m9h/freeeeg128/paper/paper.pdf

## FreeEEG128: Design and Roadmap for an Open-Hardware 128-Channel EEG Acquisition System

Historical lineage, current-state audit, and alpha/beta plan

Morgan Hough¹

1NeuroTechX., morgan.hough@gmail.com

April 2026

Abstract

We present the design state, hardware audit, and alpha-to-beta development roadmap of FreeEEG128, an open-hardware 128-channel scalp electroencephalography acquisition system evolving the NeuroIDSS FreeEEG128-alpha platform. The alpha board pairs an STMicroelectronics STM32H743ZI Cortex-M7 microcontroller with sixteen Texas Instruments ADS131M08 24-bit delta-sigma ADCs distributed across six SPI buses, a timer/DMA cascade providing sample-synchronous chip-select pulses, and a medical-grade digital- and power-isolation barrier between subject and host. The accompanying cap carries 130 dry Ag/AgCl passive electrodes on a 10/5 textile scaffold. We situate the design in the lineage running from Nunez’s biophysical framework through Gevins’ real-time cognitive-state engineering, Tucker’s Geodesic Sensor Net at Electrical Geodesics, Inc., and the active-electrode breakthrough at BioSemi; and we identify Black et al. 2017 (Open Ephys + EEG) as the primary feature-for-feature comparison benchmark. We audit the alpha board’s peripheral inventory, flag the shortcomings of the stock firmware, and present a phased firmware rewrite (packet-format freeze, modular driver layer, first-class impedance mode, device-side timestamping, watchdog and DFU support). We commit to a belt-pack wearable form factor with a cap-mounted passive brain-box; reject the STM32MP2 upgrade path due to battery-weight and EMI regressions; and plan an ESP32-S3 co-processor on a beta revision for CircuitPython-compatible networking, LSL/WebSocket delivery, and an Adafruit-ecosystem surface. Validation against the Black et al. eyes-closed alpha-vs-actiCHamp protocol is proposed as the beta acceptance gate, with integrations targeted for Open Ephys GUI, MNE-CPP, and BrainFlow on day one.

## Contents

1 Introduction | 2
2 Historical lineage | 3

3 Related open-hardware work | 5
4 System architecture | 7
5 Enclosure, form factor, and cabling | 9
6 MCU and companion-processor choice | 9
7 Firmware rewrite | 12
8 Host and application support | 12
9 Validation plan | 14
10 Open questions and next steps | 14
11 Future directions: form-factor variants | 14

## 1 Introduction

High-density electroencephalography was born from three simultaneous mid-1990s breakthroughs: Paul Nunez’s biophysical account of scalp potentials and the corresponding Nyquist-style argument for densely sampling the head [Nunez, 1981, Nunez and Westdorp, 1994]; Alan Gevins’ real-time cognitive-state engineering practice; and the first commercial 256-channel EEG system, built at Neuroscan by Pflieger and Sands [Pflieger and Sands, 1996], followed rapidly by the second 256-channel system at Electrical Geodesics, Inc. (EGI), which commercialized Tucker’s Geodesic Sensor Net [Tucker, 1993]. Three decades later, academic and clinical high-density EEG remains dominated by a handful of closed-ecosystem vendors (BioSemi, Brain Products, ANT Neuro, Compumedics Neuroscan, g.tec, NA300/GTEN, etc.), and the open-hardware movement has only recently approached 100-channel counts.
The open-hardware track itself has matured quickly. OpenBCI (2014) made 8-channel ADS1299 acquisition routinely accessible; Open Ephys (Siegle et al. 2017 [Siegle et al., 2017]) generalized 512-channel multichannel electrophysiology via a plugin GUI; Black et al. 2017 [Black et al., 2017] adapted that platform to 128-channel human EEG and validated it side-by-side against a Brain-Vision actiCHamp clinical amplifier. Cardona-Álvarez et al. 2023 [Cardona-Alvarez et al., 2023] published the most detailed production framework for an open-hardware BCI to date, built on OpenBCI Cyton with a Raspberry Pi acquisition server, distributed Kafka-based message fan-out, and a custom three-layer driver stack; their work documents the OpenBCI Cyton+Daisy 8→16 channel interleaving artifact that FreeEEG128’s synchronized 16×ADS131M08 architecture eliminates. More recent entries — PiEEG, IronBCI, HackEEG, BIOADC, Neurogate OctaFlow — cover an expanding range of channel counts, packaging, and wireless protocols, but none have delivered 128-channel density with full medical-grade isolation, free licensing of both firmware and hardware, and first-class support for the full open real-time stack (Open Ephys GUI + MNE-CPP + BrainFlow + LSL + BIDS-EEG).
FreeEEG128 aims at that gap. The alpha revision (NeuroIDSS, Vivancos 2023 [Vivancos, 2023]) exists as fewer than five physical units worldwide. One is on the author’s bench; the present paper describes the design audit, the firmware-rewrite roadmap, and the planned beta revision.

## 2 Historical lineage

### 2.1 Theoretical foundations — Nunez

Nunez’s book Electric Fields of the Brain [Nunez, 1981] (second edition with Srinivasan [Nunez and Srinivasan, 2006]) remains the canonical biophysical reference. Three arguments continue to shape hardware design: (i) scalp potential is spatially low-pass-filtered relative to cortical sources, with the skull acting as a 2 cm to 3 cm smoothing kernel; (ii) reference electrode choice is not neutral, and software-defined referencing (surface Laplacian, average reference) is required for source-localization work [Nunez and Westdorp, 1994]; and (iii) volume conduction ensures that no scalp sensor sees a single source. Each of these motivates the channel-count race of the 1990s: below roughly 64 electrodes the surface-Laplacian math does not pay off.

### 2.2 Engineering pioneer — Gevins

Alan Gevins founded EEG Systems Laboratory (1980) and SAM Technology (1986), and by the early 1990s had pushed EEG hardware practice toward 64 and 128 channels with sustained real-time cognitive-state analysis. His “deblurring” methods, combining MRI-derived geometry with scalp EEG to estimate cortical-surface potential [Gevins et al., 1997], predate modern source localization and established the protocol templates for sustained-attention and mental-workload studies that the field still uses.

### 2.3 Engineering breakthrough — Tucker and EGI

Don Tucker’s Geodesic Sensor Net [Tucker, 1993], commercialized as Electrical Geodesics, Inc., is the direct ancestor of the FreeEEG128 form factor. The saline-sponge electrode array on a tension-distributed elastic polymer scaffold solved the practical application-workflow problem that had made high-density EEG impractical outside specialist labs: application time dropped from 60+ minutes (paste-based) to approximately five minutes. EGI built the second 256-channel EEG system in the world; the present author served as its first software engineering manager during the mid-1990s. Ramesh Srinivasan, Nunez’s co-author on the second edition of Electric Fields of the Brain [Nunez and Srinivasan, 2006] and now Professor of Cognitive Sciences and Biomedical Engineering at UC Irvine, was an early member of EGI, which is why EGI’s product line shipped with surface-Laplacian and average- reference montaging as first-class software features from the start.

### 2.4 The commercial high-density era

Table 1 summarizes the commercial high-density landscape. Common themes that FreeEEG128 inherits, or explicitly moves past, include a pervasive reliance on proprietary caps, connectors, amps, and software; the emergence of belt-pack amps (ANT, BrainProducts LiveAmp) after a decade of desk-tethered designs; the first high-density active-electrode system at BioSemi in the late 1990s, which remains the standard against which movement-tolerant recording is measured; and the eventual standardization of per-channel impedance-check and reference- flexibility as tablestakes features.

Table 1: Representative commercial high-density EEG vendors. Channel counts are the maxima offered; years are approximate first-introduction.

Vendor | System | Max ch | Era | Notable feature
Neuroscan | SynAmps / Quik-Cap | 256 | early 1990s | First 256-ch system [Pflieger and Sands, 1996]
EGI | Net Amps / Geodesic Sensor Net | 256 | 1992- | Saline-sponge quick-apply cap
BioSemi | ActiveTwo | 256 | late 1990s- | First HD-EEG with active electrodes
BrainProducts | actiCHamp / actiCAP | 256 | 2000s- | BrainVision Recorder ecosystem
ANT Neuro | eego / Waveguard | 256 | 2000s- | Belt-pack amp + dry-alt caps
Compumedics Neuroscan | SynAmps2 / SynAmpsRT | 512 | 2000s- | Clinical mainstay
g.tec | g.USBamp / g.Nautilus | 256 | 2000s- | Modular headbox
g.tec | g.Pangolin / g.HIamp (4×) | 1024 | 2023- | VHD-EEG SOTA flex-PCB active-wet grids; 8.6 mm spacing; 95.2% CS localization vs ECoG [Schreiner et al., 2024]

### 2.5 The very-high-density frontier — g.Pangolin and 1024-channel EEG

A second revolution has been quietly underway since roughly 2020: the move from “HD-EEG” (64–128 channels) to ultra- or very-high- density EEG (VHD-EEG / uHD-EEG, 256–1024+ channels). The theoretical driver is a refinement of Nunez’s spatial-Nyquist argument — Grover and Venkatesh (cited in Schreiner et al. 2024) propose, on information-theoretic grounds, that the scalp’s spatial bandwidth demands not hundreds but thousands of electrode positions to capture all of the information it carries.
The state-of-the-art commercial VHD system is g.tec’s g.Pangolin [Schreiner et al., 2024], a 1024-channel-capable uHD-EEG platform operating at a 256-channel density in the published demonstration. Key specifications:
- Up to 1024 channels via four g.HIamp 256-channel amplifiers.
- Flexible printed-circuit electrode grids of 16 channels each, with gold-plated electrode points arranged at 8.6 mm inter-electrode distance and 5.9 mm electrode diameter.
- An active pre-amplifier per grid (fixed gain 10) before the back-end g.HIamp.
- Wet electrodes with conductive paste (Elefix) under an adhesive layer designed to prevent bridging and crosstalk.
- 24-bit ADC resolution, up to 38.4 kHz sample rate per channel.
- Authors of Schreiner et al. (2024) include Christoph Guger (founder of g.tec) among g.tecaffiliated researchers.

Schreiner et al. use this system at 256-channel density to demonstrate 95.2% classification accuracy of channels as anterior or posterior to the central sulcus via somatosensory-evokedpotential phase-reversal analysis — a level of functional precision previously only achievable with surgically implanted ECoG.
Closely related theoretical and methodological work includes Shirazi, Onton & Makeig (2025) [Shirazi et al., 2025], who simulate scalp EEG from ultra-high-density ECoG to quantify cortex-to-scalp projection patterns; Liu et al. (2018) [Liu et al., 2018], who establish the systematic benefits of density, head modeling, and source localization for reconstructing large-scale brain networks; and Fiedler et al. (2022) [Fiedler et al., 2022], whose 256-channel dry cap covers the dry-electrode side of the VHD spectrum.

Where FreeEEG128 sits in this landscape. We are deliberately not claiming VHD-EEG status. The open-hardware frontier at 256+ channels remains commercial-only as of April 2026. FreeEEG128 occupies the “affordable mid-density open-hardware” niche: higher channel count than OpenBCI (8–16) and Open Ephys + EEG / Black 2017 (64–128), lower than g.Pangolin (1024), at roughly one to two orders of magnitude lower cost than the commercial systems at comparable channel counts. A natural upgrade path (“FreeEEG256”) on the same STM32H743 + ADS131M08 chassis is plausible — thirty-two ADCs across six SPI buses plus a second- stage cable design — and would put open hardware meaningfully closer to the VHD threshold, but that is explicitly not within the present roadmap.

### 2.6 The open-hardware generation

FreeEEG128 sits at the current frontier of open-hardware EEG. Section 3 presents the feature-level comparison in detail.

## 3 Related open-hardware work

Table 2 enumerates the open-hardware EEG projects relevant to FreeEEG128. Two observations matter for design decisions. First, no existing open-hardware project reaches 128 channels without compromising on either licensing (Black et al. 2017 is CC-BY-NC-SA 3.0 IGO, restricting commercial use) or form factor (every 128+ ch system is desk-tethered rather than wearable). Second, the industry-default single-chip ADC for these projects is the Texas Instruments ADS1299 (eight channels, 24 bit); FreeEEG128-alpha instead uses sixteen ADS131M08s, inheriting the FreeEEG32-beta demonstration that this chip family achieves research-grade noise performance at lower cost.

Table 2: Open-hardware EEG boards relevant to FreeEEG128. “Ch” = channels; “Res” = ADC resolution
in bits; “SR” = maximum sample rate.
Project | MCU | ADC | Ch | Res | SR (Hz) | Host I/F | License | Lineage / note
OpenBCI Cyton | PIC32MX | ADS1299 | 8 (16 w/ Daisy) | 24 | 250 | BLE+USB | MIT | Reference packet format
OpenBCI Ganglion | nRF51822 | MCP3912 | 4 | 24 | 200 | BLE | MIT | BLE-direct
OpenBCI Galea | i.MX RT1062 | multi-1299 | 8 + aux | 24 | 500 | USB-C | closed HW | Multimodal in HMD
HackEEG | SAM3X8E (Due) | ADS1299 | 8–32 | 24 | 16 k | USB | MIT | JSONLines/MessagePack dual
PiEEG | Pi SPI-HAT | ADS1299 | 8 / 16 | 24 | 500 | (host Pi) | GPL-3.0 | Host-as-MCU pattern
IronBCI | STM32F4 | ADS1299 | 8 | 24 | 500 | USB + BLE | GPL-3.0 | Validated vs BioSemi
BIOADC | PIC32 | ADS1299 | 32 | 24 | 500 | USB | CC | Full open schematic [Gargiulo et al., 2019]
Neurogate OctaFlow | ESP32-C3 | ADS1299 | 8 | 24 | 4 k | USB + Wi-Fi | open | Adafruit-ecosystem MCU
FreeEEG32-beta | STM32F4 | 4×ADS131M08 | 32 | 24 | 2 k | USB | AGPL-3.0 | ADS131M08 proving ground
Open Ephys + EEG | Opal Kelly FPGA | Intan RHD2132/2164 | up to 128 | 16 | 30 k | USB 3.0 | CC-BY-NC-SA 3.0 IGO | Black et al. 2017 [Black et al., 2017]
FreeEEG128 | STM32H743ZI | 16×ADS131M08 | 128 | 24 | 32 k cap | USB-CDC (FS) | AGPL-3.0 + CERN-OHL-S (planned) | this work

### 3.1 Primary benchmark: Black et al. 2017

Black et al. [Black et al., 2017] adapt commercial EEG caps onto the Open Ephys acquisition board via a custom breakout-to-Omnetics-to-Intan- headstage chain. The abstract reports: “The Open Ephys + EEG system can record reliable human EEG data, as well as human EMG data. A side-by-side comparison of eyes closed 8–14 Hz activity between the Open Ephys + EEG system and the Brainvision ActiCHamp EEG system showed similar average power and signal to noise.” Three consequences for FreeEEG128 design follow directly:

- Validation protocol. Eyes-closed 8–14 Hz alpha power and SNR, side-by-side against a Brain-Vision actiCHamp clinical amplifier, is the minimum bar to call anything “beta.” We adopt it verbatim as the FreeEEG128-beta acceptance gate (Section 9).
- Commercial-cap adapter pathway. Their breakout-PCB model is a template for a sister FreeEEG128-amp variant that accepts any commercial EasyCap-class cap. Worth prototyping after the beta lands.
- Plugin-GUI integration. Their stack is native to the Open Ephys GUI. We plan an equivalent acquisition plugin for FreeEEG128, and the corresponding native plugin for MNE Scan (Section 8).

Table 3 gives the feature-level comparison.

Table 3: FreeEEG128 vs Open Ephys + EEG (Black et al. 2017)

Axis | Open Ephys + EEG | FreeEEG128
ADC / amplifier | Intan RHD2132 / RHD2164
bioamp, 16-bit SPI

16× TI ADS131M08, 24-bit ∆Σ

Channels | 32 | / | 64 | / | up | to | 128
(2×RHD2164); | board | max
| 512

128 fixed

Sample rate | Configurable to 30 kHz (Intan
max)

250 Hz firmware default; chip supports up to ∼32 kSPS
Resolution | 16 bits | 24 bits
Input-ref noise | ∼2.4 µV RMS (Intan RHD spec) ∼0.5 µV RMS over 250 Hz BW
at gain 32
Acq. board | Open Ephys board: Opal Kelly
XEM-6310 FPGA, USB 3.0
Custom | FreeEEG128 | PCB:
STM32H743ZI | + | on-board
ADS131M08 bank; no FPGA
Host interface | USB 3.0 from Open Ephys board | USB-CDC (FS, via ADuM3160);
beta | adds | Wi-Fi/BLE | via
ESP32-S3
Cap / electrodes | Commercial | EasyCap-
class | via | custom
breakout→Omnetics→RHD
headstage

Open-hardware 130-electrode dry Ag/AgCl cap; cap is part of the project

Reference / gnd | Configurable via breakout | CP1 = ref, CP2 = gnd (hard-
wired at alpha)

Axis | Open Ephys + EEG | FreeEEG128
Isolation | Partial; Open Ephys board is USB-mains-referenced unless iso-
| lated upstream

Full medical-grade on-board: ADuM3160 + ADuM1402 + 2×
ISO7341C + SN6505B+xfmr
Form factor | Desk / rack | Belt-pack | wearable | (Sec-
| | tion 5)
Stimulus sync | 8 DI + 8 DO + 8 ADC + 8 DAC
| on Open Ephys board

Currently none; beta plan = TTL via ADuM1402 spare lane + Labstreamer
Total cost est. | ∼USD 2000–3500 | ∼USD 500–1000 BOM
License | CC-BY-NC-SA 3.0 IGO (non- commercial)
AGPL-3.0 firmware + CERN-OHL-S-v2 hardware (planned)

## 4 System architecture

### 4.1 Alpha board overview

Figure 1 diagrams the alpha acquisition chain. One hundred thirty passive dry Ag/AgCl electrodes on a 10/5-system textile cap (DC resistance ≤ 500 Ω, 12 mm diameter, multi-prong) terminate in 1.5 mm DIN touch-proof plugs that mate into a custom passive brain-box. The brain-box fans the 128 channels (128 signal + CP1 reference + CP2 ground) into sixteen Texas Instruments ADS131M08 ∆Σ ADCs [Texas Instruments, 2020], eight channels per chip, arranged with a deliberately scrambled mapping that assigns topographically distant electrodes to the same ADC package in order to maximize across-ADC signal independence. The ADCs run at gain 32, reference voltage 1.25 V, and an on-board firmware-configured sample rate of 250 Hz.

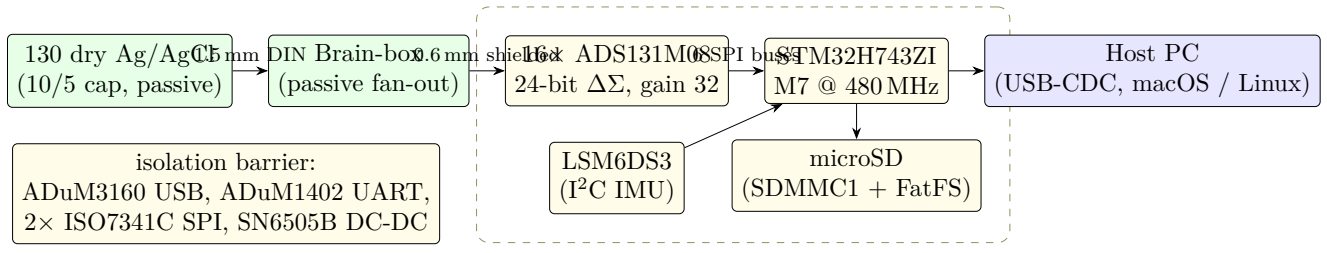
[picture p1: figure]
130 dry Ag/AgCl (10/5 cap, passive); Brain-box (passive fan-out); 16× ADS131M08 24-bit ∆Σ, gain 32; STM32H743ZI M7 @ 480 MHz; microSD (SDMMC1 + FatFS); LSM6DS3 (I²C IMU); isolation barrier: ADuM3160 USB, ADuM1402 UART, 2× ISO7341C SPI, SN6505B DC-DC; Host PC (USB-CDC, macOS / Linux); 1.5 mm DIN; 0.6 mm shielded; 6 SPI buses

Figure 1: FreeEEG128-alpha acquisition chain. The dashed boundary delimits the galvanically isolated patient-side subsystem; USB and programming interfaces cross the barrier via digital isolators (ADuM), while power crosses via a push-pull transformer DC-DC.

### 4.2 Microcontroller and clocking

The STM32H743ZI [STMicroelectronics, 2024] (Cortex-M7 at 480 MHz, 2 MB flash, 1 MB SRAM, double-precision FPU) is the correct choice for this system and is retained across the alpha→beta transition (Section 6). Three capabilities explain why no other microcontroller in the Adafruitsupported ESP32 lineage or the Cortex-M4 cost-down tiers would work: (i) six independent SPI peripherals, required to read sixteen ADS131M08s without daisy-chain penalties; (ii) a TIM1/TIM8 cascade routed through DMA in circular mode onto a GPIO port, generating sample-synchronous chip-select pulses across all sixteen chips with zero CPU involvement; and (iii) a radio-quiet substrate and low-jitter clock tree adjacent to a 24-bit ∆Σ analog front-end.
An external FXO-SM7 oscillator drives the ADC master clock. The STM32’s HSE is a 16 MHz crystal and an LSE 32.768 kHz crystal is populated for RTC use (currently unused by the stock firmware).

### 4.3 Isolation and power

The board implements a textbook medical-isolation topology. On the digital side, an Analog Devices ADuM3160 full-speed USB isolator gates the host link; an ADuM1402BRWZ quad digital isolator handles the SPI/UART path to the programming headers; and two ISO7341C 3-channel isolators sit on the SPI fabric that reaches the ADC bank. On the power side, a Texas Instruments SN6505B push-pull transformer driver feeds a Würth 750315371 transformer, producing the isolated 5 V analog island; this is then regulated by three Texas Instruments LP5907 ultra-low-noise LDOs (6.5 µV RMS, ∼82 dB PSRR at 1 kHz) generating AVDD, VDD, and IOVDD, with an Analog Devices ADP7118 serving as an alternate high-PSRR LDO. Voltage references are supplied by a REF2025 (ADC Vref) and an ADR4525 (precision reference). The upstream USB rail is deliberately a non-critical rail, which is why the stock firmware can operate adequately from a consumer USB power bank.

### 4.4 Peripheral-by-peripheral audit

Table 4 summarizes the STM32 peripherals presently configured in the stock firmware’s .ioc file, cross-referenced against Src/main.c:2237–2255. Notable findings for the firmware rewrite include:
(i) the D-Cache is disabled, a workaround for cached DMA-buffer staleness which we will replace with an MPU-backed non-cacheable region; (ii) the .ioc simultaneously configures USB_DEVICE and USB_OTG_HS, with the virtual-pin assignment labeling the device VS_USB_DEVICE_CDC_HS, but PB14/PB15 are set to Device_Only_FS — an HS-versus-FS conflict that will be resolved by locking to FS because the ADuM3160 isolator is full-speed only; (iii) legacy ad7779.c/h files from the FreeEEG32 predecessor remain in the tree, and commented-out W5500 (WIZnet SPI-to-Ethernet) bring-up code from FreeSmartEEG is present but unused; and (iv) neither the IWDG watchdog nor the RTC is initialized, despite the LSE crystal being populated.

Table 4: Stock-firmware peripheral inventory (from .ioc and main.c).

STM32 IP | Allocation | DMA
SPI1 – SPI6 (six buses) | ADS131M08 bank | SPI2/3/4/5 via DMA1/2
I
2C1 | LSM6DS3 IMU | –
I
2C2 | spare | –
SDMMC1 | microSD + FatFS | native controller
USART1 | Isolated UART (ADuM1402) — debug printf | –
TIM1 | Sample-sync CS pulse generator (TRGO → DMA) | DMA1 Stream 7, Circular
TIM8 | Clock source for TIM1 cascade (TRGO) | DMA1 Stream 4, Circular
USB (FS) CDC | Host data link via ADuM3160 | –
DMA1 + DMA2 + MDMA | SPI traffic + TIM cascades | enabled
IWDG / WWDG | not configured | –
RTC (LSE 32.768 kHz) | not used | –

## 5 Enclosure, form factor, and cabling

At 128 channels the device cannot reasonably be head-worn. The 130-lead harness, plus the 1.5 mm DIN connector field, plus a battery and amp PCB exceeds a wearable head-mount mass and volume budget by an order of magnitude; every commercial high-density system at 128 channels or above solves this the same way (belt-pack or shoulder-pack amp, bundled shielded cable to a cap-mounted passive fan-out). The FreeEEG128-beta form factor accepts this:

Cap (head-worn): 130 dry electrodes → 130× 1.5 mm DIN
↓
Brain-box (cap-mounted, passive fan-out)
↓
1–2 multipole quick-disconnect (HD D-sub HD78 or LEMO EGG.4B) ↓ 30–60 cm shielded bundle
Amp box (belt-pack): FreeEEG128 PCB + battery
↓ USB-CDC (or Wi-Fi on beta) Host PC

Battery chemistry is flexible because the ADuM3160 + SN6505B + LP5907 chain already rejects upstream ripple at audio frequencies. The alpha stays with a consumer USB power bank; the beta plans a 2S 18650 Li-ion pack with an ideal-diode OR between USB-C input and pack, and an LT3045 class ultra-low-noise LDO for the input rail. A Samsung PRO Endurance microSDXC is recommended for sustained write loads; the stock firmware’s FatFS is configured for FAT32, so SDXC cards must be reformatted before first mount.
The beta-rev connector strategy is HD D-Sub HD78 at the brain-box↔amp break, retaining the 1.5 mm DIN at the electrode end for subject-contact safety. Two HD78 shells cover 130 leads; the metal shell provides a known-good shield reference and cleanability, and any clinical technician can mate them. An upgrade path to LEMO EGG.4B multipole connectors is open for a clinical-grade variant.

## 6 MCU and companion-processor choice

We evaluated upgrade paths from the current STM32H743ZI. Table 5 summarizes. The verdict: retain H743 as the acquisition engine; treat STM32N6 as the only interesting STM32 upgrade (for on-device ML via the Neural-ART NPU); reject STM32MP2 as wrong-tool- for-task; and add an ESP32-S3 co-processor on the beta board to deliver Wi-Fi/BLE, CircuitPython compatibility, STEMMA QT / Adafruit sensor ecosystem access, and native LSL/WebSocket publishing.

Why ESP32 cannot replace the STM32. A full swap to an ESP32-S3 or ESP32-P4 fails on three technical axes: SPI bus count (S3 has 2 usable vs our requirement of 6; P4 has 3); absence of the TIM-cascade-to-DMA-to-GPIO sample-sync primitive; and WiFi radio emissions coupling into a 24-bit ∆Σ analog front-end. These objections do not apply to an 8-channel teaching board such as Neurogate OctaFlow, which is why ESP32-C3 is correct there. For 128-channel medical- grade acquisition the STM32 is the right silicon.

### 6.1 Companion processor for the beta revision — Raspberry Pi Zero 2W

The alpha board communicates with a host computer via USB-CDC. The beta revision needs to add wireless host connectivity, on-device scripting, LSL / BrainFlow / MNE-Python availability,

Table 5: STM32 upgrade evaluation. Pricing and SKU availability should be re-verified with current distributor data.

Option | Clock | Key delta vs H743 | Verdict
STM32H753ZI | 480 MHz | + crypto accelerator | No; crypto on ESP32-S3
STM32H723/H725ZG | 550 MHz | +15%, less RAM | No; RAM regression
STM32H7A3/B3ZI | 280 MHz | 2 MB | flash | + | 1.4 MB
RAM, USB-HS PHY

Marginal

STM32H755/H757ZI | 480+240 MHz | M7 + M4 dual-core | No; doesn’t give Adafruit alignment
STM32H7R / H7S | 600 MHz | XiP-flash architecture | No
STM32N6 | 800 MHz | Cortex-M55 + Helium
+ on-die NPU

Consider if on-device ML wanted

STM32MP2 | A35 Linux + M33 | Runs Linux on-chip | No; 10× battery-weight regression, HDI PCB required, EMI concerns

and an operator-facing web UI, so that the whole system can be carried in a shoulder-strap pack
and used without a tethered laptop. We considered two architectures for this companion:
1. An on-PCB ESP32-S3 co-processor connected to the STM32H743 over isolated SPI, running ESP-IDF or CircuitPython, re-emitting the framed EEG stream over Wi-Fi/BLE/WebSocket/LSL.
2. A Raspberry Pi Zero 2W (quad-core Cortex-A53, 512 MB RAM, dual-band Wi-Fi, BLE 5) sharing the enclosure with the FreeEEG128 PCB, connecting over plain USB-CDC, running Raspberry Pi OS 64-bit Lite with the full Python stack pre-installed.

Table 6 compares the two paths. We adopt option 2.

Table 6: Companion-processor trade study.

Factor | ESP32-S3 on-PCB | Raspberry Pi Zero 2W
Additional firmware project | ESP-IDF or CircuitPython, ∼2–
4 weeks

None stock Raspberry Pi OS

Native Python / pylsl / Brain-Flow / MNE-Python

Requires porting or staged progression

Day one via pip install

Algorithm iteration on-device | No (recompile + flash) | Yes (SSH + Python REPL)
Operator web UI | Would need to write | FastAPI + browser in a day
STM32 ↔ host link | New isolated SPI bridge + isola-
tor design
USB-CDC | on | existing
ADuM3160
MNE-CPP integration | Requires Stage 2 native plugin | Stage 1 LSL loopback suffices
Average power | ∼0.75W | ∼1.25W
Boot time | Instant | 15–30 s (mitigated by auto-start)
PCB footprint | 25×18 mm module | 65×30 mm SBC
Storage | On-chip flash | microSD + optional USB drive
Adafruit-ecosystem pedagogy | CircuitPython native | Via Blinka shim on Linux

The decisive points are the elimination of the second firmware project (deleting two to four weeks of work from the beta critical path) and the removal of the staged MNE-CPP integration complexity. The 50% power-draw increase is tolerable — a 2S 18650 pack (25 Wh) still gives 6–8 h of session at total system draw ∼3–4 W, which is more than enough for typical research paradigms. The boot-time concern is mitigated by configuring systemd to auto-start the capture and LSL services on boot, and by adding a small e-ink status strip to the enclosure so the operator sees when the device is ready.

### 6.2 Pre-validation with synthetic data on the Pi Zero 2W

A significant advantage of the SBC architecture is that the entire host stack can be validated with simulated EEG data before the FreeEEG128 firmware rewrite completes. We plan the following benchmark suite to run on the Pi Zero 2W in advance of alpha bring-up:

1. Base Python speed: NumPy FFT on a 128×25 000 complex array; target under 50 ms.
2. LSL local loopback: an outlet and inlet pair in the same process pushing 128-channel float32 samples at 250 Hz; measure pull latency and sustained throughput for 60 s.
3. BrainFlow SYNTHETIC_BOARD: stream synthetic EEG for 5 min via BrainFlow; confirm zero sample drops.
4. EEG-ExPy packaged experiments: run NeuroTechX EEG-ExPy’s Visual P300, SSVEP, and N170 paradigms with the synthetic backend; confirm experimental loop completes without dropped frames.
5. MNE-Python online preprocessing: filter and ICA on a 5-minute synthetic epoch; time and memory profile.
6. BIDS-EEG writer: write a synthetic dataset out to BIDS and verify with the BIDS validator.
7. Wall-power draw: 10-minute LSL loopback measured at a USB power meter; confirms the battery-life budget above.

When the FreeEEG128 firmware is ready, the only change to the host stack is swapping the BrainFlow synthetic-board backend for the real-device backend. Everything downstream (LSL outlet, MNE processing, EEG-ExPy paradigm hooks, BIDS writer, web UI) is validated and stable.

### 6.3 Optional: OpenWrt router as a recording appliance

For portable-lab deployments and multi-client recording scenarios, an OpenWrt-based Wi-Fi router (e.g., GL.iNet GL-MT3000 “Beryl AX”, ∼USD 80, pocketable, USB 3 port, Wi-Fi 6) can be added as a dedicated network appliance between the Pi-borne FreeEEG128 and one or more recording / analysis laptops. OpenWrt provides:

- A dedicated SSID (“EEG-NET”) with zero extraneous traffic, eliminating LSL UDP packet loss under lab network contention.
- Router-enforced QoS prioritizing LSL traffic.
- A system-wide NTP (or, with compatible hardware, PTP) authority, providing a common time base across all clients with faster convergence than pure LSL time correction.
- Packet-level recording redundancy: a lightweight sniffer service on the router can dump LSL traffic to a USB stick, so the stream is preserved even if a recording laptop crashes.
- WireGuard / OpenVPN ingress for remote monitoring, keeping the subject’s recording network off the venue infrastructure.

For single-subject bench recordings with one laptop, the router adds complexity with little benefit and can be skipped (the Pi can run as a Wi-Fi access point directly). The architecture earns its keep in field deployments, hyperscanning paradigms, and any recording session that must be independent of venue Wi-Fi. OpenWrt is deliberately optional in the roadmap; the Pi-and-laptop baseline is the default.

## 7 Firmware rewrite

The stock alpha firmware was written against STM32CubeMX 1.5.1 in approximately 2021–2022. It demonstrates working communication with all sixteen ADS131M08 chips at 250 Hz and emits raw 24-bit samples over USB-CDC to a host. It is, however, fundamentally research-prototype quality. Table 7 summarizes the planned rewrite.

## 8 Host and application support

We target the full open real-time EEG stack on day one of the beta release:
Host-side software runs on the beta’s Pi Zero 2W companion (Section 6.1), with Raspberry Pi OS 64-bit Lite as the base operating system.

Lab Streaming Layer (LSL). Python host publishes an LSL outlet per device; Labstreamer TTL markers ingest as a second LSL stream.

BrainFlow. We write and upstream a Board definition, which pulls in MNE-LSL, LabRecorder, Timeflux, NeuroPype, and OpenViBE for free.

Open Ephys GUI. An acquisition plugin, modeled on the Rhythm Node, ingests FreeEEG128 frames into the Open Ephys GUI plugin architecture.

MNE-CPP / MNE Scan. Three-stage integration. Stage 1 is free via LSL loopback through MNE Scan’s existing LSL adapter. Stage 2 is a native freeeeg128adapter plugin modeled on applications/mne_scan/plugins/lsladapter/ and upstreamed via PR. Stage 3 adds FIFF writing in the Python host so that MNE-Python users read captures via mne.io.read_raw_fif() with no translation layer.

BIDS-EEG. Python host writes BIDS-compliant datasets with event markers and per-channel impedance metadata.

EEG-ExPy. NeuroTechX’s EEG-ExPy paradigm library (neurotechx.github.io/eeg-expy) provides packaged implementations of Visual P300, SSVEP, N170, and auditory-oddball experiments. These are used for the pre-validation benchmarks in Section 6.2 and remain available as ready-to-run paradigms for users of the finished device.

Operator web UI. A FastAPI application on the Pi serves a browser-based session control and quality-monitoring dashboard, so that the subject’s device needs no tethered laptop during a recording session.

### 8.1 Comparison-plot

Figure 2 places FreeEEG128 against the open-hardware landscape on the channel-count versus

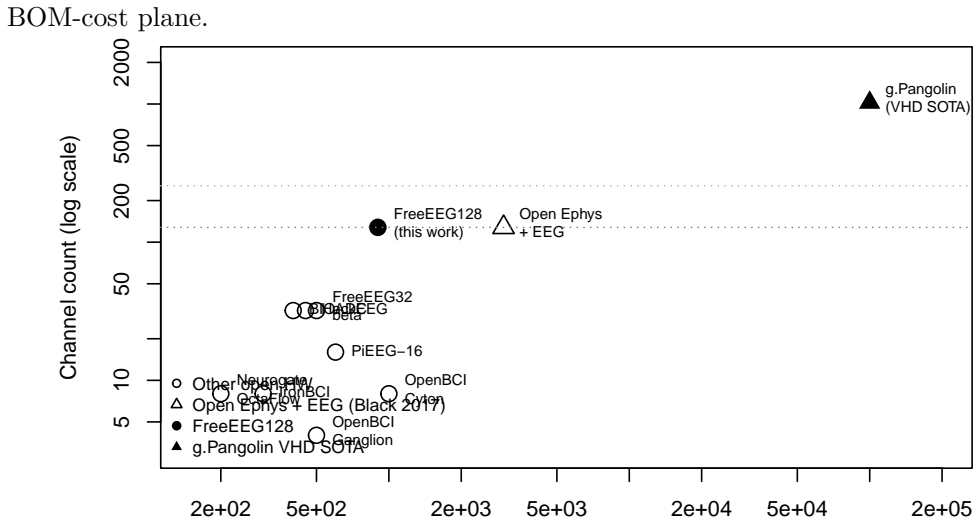
[picture p2: figure]
BOM-cost plane.; Channel count (log scale); OpenBCI Cyton; OpenBCI Ganglion; HackEEG; PiEEG−16; IronBCI Neurogate OctaFlow; BIOADC; FreeEEG32 beta; Open Ephys + EEG; FreeEEG128 (this work); g.Pangolin (VHD SOTA); Other open HW Open Ephys + EEG (Black 2017) FreeEEG128 g.Pangolin VHD SOTA

Estimated BOM / retail cost (USD, log scale)

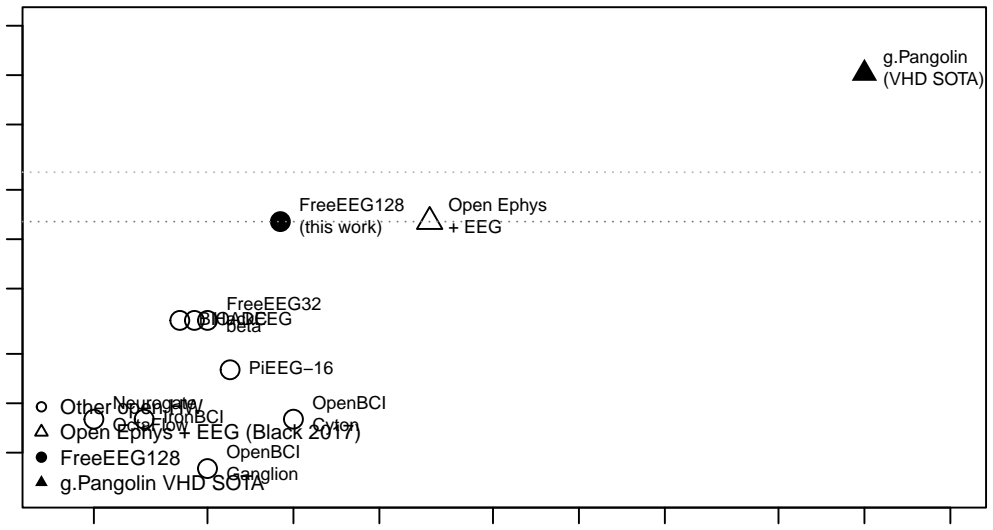
[picture p3: figure]
OpenBCI Cyton; OpenBCI Ganglion; HackEEG; PiEEG−16; IronBCI Neurogate OctaFlow; BIOADC; FreeEEG32 beta; Open Ephys + EEG; FreeEEG128 (this work); g.Pangolin (VHD SOTA); Other open HW Open Ephys + EEG (Black 2017) FreeEEG128 g.Pangolin VHD SOTA

2e+02 | 5e+02 | 2e+03 | 5e+03 | 2e+04 | 5e+04 | 2e+05

5 10 50 200 500 2000

### Estimated BOM / retail cost (USD, log scale)

### Channel count (log scale)

Figure 2: Open-hardware EEG landscape on the channel-count vs. cost plane, with g.Pangolin [Schreiner et al., 2024] added as the commercial VHD-EEG state-of-the-art reference point. FreeEEG128 and Open Ephys + EEG (Black et al. 2017) are the only 128-channel open entries; FreeEEG128 achieves this at approximately one-third the cost of Open Ephys + EEG and with 24-bit ADC resolution versus the Intan RHD family’s 16-bit. g.Pangolin demonstrates the VHD-EEG frontier at roughly 10²–10³
times the cost.

## 9 Validation plan

The acceptance gate for calling anything “beta” is a direct replication of Black et al. [Black et al., 2017]: eyes-closed 8–14 Hz alpha power and SNR, side-by-side against a BrainVision actiCHamp (or another clinical-grade reference amplifier). The same subject, the same room, the same electrode montage where possible. We report per-channel average power and broadband SNR matching the Black paradigm, plus the drop-counter and impedance metadata that the firmware rewrite delivers. Raw data and analysis notebooks are published under docs/validation/ at the same moment the beta schematic is released.
Secondary validation targets, sequenced after the acceptance gate: an auditory-oddball P300 latency confirmed within 20 ms against a Labstreamer photodiode/TTL ground truth; a steadystate visual evoked potential (SSVEP) spectrum at 6, 7.5, 10, and 15 Hz; and a resting-state connectivity replication against one of the large publicly available datasets.

## 10 Open questions and next steps

Open items that require decisions during Phase B0 of the beta rev:

1. Black’s Brain Topography DOI for Tucker 1993 — currently cited from Tucker’s 1993 Electroencephalography and Clinical Neurophysiology paper; check whether there is a better primary for the Geodesic Sensor Net.
2. Whether to enable the Neural-ART NPU via STM32N6 on the beta, or keep STM32H743 and plan on-device ML only as a software add-on.
3. Whether the FreeEEG128 hardware license moves from the upstream NeuroIDSS AGPL-3.0 to CERN-OHL-S-v2 (strongly recommended; AGPL is a software license and is legally murky on hardware).
4. Connector choice for the brain-box↔amp link: HD D-Sub HD78 (budget path) or LEMO EGG.4B (clinical-grade path).
5. Whether to reproduce Black et al.’s commercial-cap adapter chain as a sister FreeEEG128-amponly product for users with existing EasyCap hardware.
6. Whether to ship a reference OpenWrt configuration (Section 6.3) for portable-lab deployments, or leave that to users.

Immediate next steps (this week): power-on and enumeration check of the alpha unit in hand; baseline noise-floor and eyes-closed alpha capture with the stock firmware; STM32 pin audit to freeze the pinout before any firmware changes; lock the wire-packet and command-protocol specs as the alpha→beta carry-over artifacts.

## 11 Future directions: form-factor variants

The STM32H743 + 16×ADS131M08 + framed-packet stack developed here is not specific to a 128-channel cap. The same firmware, same host Python package, same wire protocol, and same LSL outlet all work at other channel counts because the CAPABILITIES packet (§3) carries n_eeg_channels and the full label list on every boot. Two spin-off directions are captured in the project roadmap:

FreeEEG-Ear — concealed around-the-ear form factor. Knierim et al. [Knierim et al., 2021, 2022] demonstrate that an open-hardware ADS1299-class amplifier connected to cEEGrid [Debener et al., 2015] around-the-ear flex-PCB electrodes captures clinical-grade EEG at ~10–20 channels per ear with electrode application times under one minute and no hair preparation. Paired with the Fastball paradigm [Stothart et al., 2017, 2021] — a 3 Hz rapid serial visual presentation with
an embedded 0.6 Hz oddball producing a passive implicit-recognition response in under three minutes — this form factor opens a screening-grade clinical pathway (dementia, stroke, paediatric memory assessment) that is not addressable by a 128-channel research rig. Hardware changes from FreeEEG128 are confined to the cap-side connector and a reduced ADS131M08 count; the firmware source tree and host stack port unchanged.

FreeEEG256 — density upgrade into the VHD class. 32×ADS131M08 across the same six SPI buses, same MCU, same isolation topology. Moves into the very-high-density class alongside g.Pangolin (§2.5) while remaining open hardware. Not on the near-term roadmap but the firmware and host work done for FreeEEG128 port forward unchanged.
The key enabling property for both is that the protocol is cap-agnostic: the CAPABILITIES descriptor turns any variant into a self-describing device the host stack recognizes without recompilation.

## Acknowledgments

The intellectual and engineering lineage of this project is long. Paul Nunez and Alan Gevins laid the theoretical and practical foundations of high-density and high-resolution EEG. Don Tucker built the Geodesic Sensor Net and with it the form factor this system inherits; Ramesh Srinivasan carried the Nunez biophysical framework into EGI’s product line. M.E. Pflieger and S.F. Sands at Neuroscan built the first 256-channel system. The entire open-hardware generation — Joel Murphy and Conor Russomanno at OpenBCI, Josh Siegle and Jakob Voigts at Open Ephys, Adam Feuer at HackEEG, Gaetano Gargiulo at BIOADC, Ildar Rakhmatulin at PiEEG/IronBCI, David Vivancos at NeuroIDSS/FreeEEG — made this project thinkable.

## References

Paul L. Nunez. Electric Fields of the Brain: The Neurophysics of EEG. Oxford University Press, New York, 1981.

Paul L. Nunez and A. F. Westdorp. The surface Laplacian, high resolution EEG and controversies. Brain Topography, 6(3):221–226, 1994. doi: 10.1007/BF01187712.

M. E. Pflieger and S. F. Sands. 256-channel ERP information growth. NeuroImage, 3(3, Supplement):S10, 1996. doi: 10.1016/S1053-8119(96)80012-7.

Don M. Tucker. Spatial sampling of head electrical fields: the geodesic sensor net. Electroencephalography and Clinical Neurophysiology, 87(3):154–163, 1993. doi: 10.1016/0013-4694(93)90121-B.

Joshua H. Siegle, Aarón Cuevas López, Yogi A. Patel, Kirill Abramov, Shay Ohayon, and Jakob Voigts. Open Ephys: an open-source, plugin-based platform for multichannel electrophysiology. Journal of Neural Engineering, 14(4):045003, 2017. doi: 10.1088/1741-2552/aa5eea.

Christopher Black, Jakob Voigts, Uday Agrawal, Max Ladow, Juan Santoyo, Christopher Moore, and Stephanie Jones. Open Ephys electroencephalography (Open Ephys + EEG): a modular, low-cost, open-source solution to human neural recording. Journal of Neural Engineering, 14(3): 035002, 2017. doi: 10.1088/1741-2552/aa651f.

Y. N. Cardona-Alvarez, A. M. Álvarez-Meza, D. A. Cárdenas-Peña, G. A. Castaño-Duque, and
G. Castellanos-Dominguez. A novel OpenBCI framework for EEG-based neurophysiological experiments. Sensors, 23(7):3763, 2023. doi: 10.3390/s23073763.

David Vivancos. MindBigData 2023 MNIST-8B: The 8 billion datapoints multimodal dataset of brain signals. arXiv:2306.00455, 2023. URL https://arxiv.org/abs/2306.00455.

Paul L. Nunez and Ramesh Srinivasan. Electric Fields of the Brain: The Neurophysics of EEG. Oxford University Press, 2nd edition, 2006.

A. Gevins, M. E. Smith, L. McEvoy, and D. Yu. High-resolution EEG mapping of cortical activation related to working memory. Cerebral Cortex, 7(4):374–385, 1997. doi: 10.1093/cercor/7.4.374.

Leonhard Schreiner, Michael Jordan, Sebastian Sieghartsleitner, Christoph Kapeller, Harald Pretl, Kyousuke Kamada, Priscella Asman, Nuri F. Ince, Kai J. Miller, and Christoph Guger. Mapping of the central sulcus using non-invasive ultra-high-density brain recordings. Scientific Reports, 14:6527, 2024. doi: 10.1038/s41598-024-57167-y.

Seyed Yahya Shirazi, Julie Onton, and Scott Makeig. Simulating scalp EEG from ultrahigh-density ECoG data illustrates cortex to scalp projection patterns. bioRxiv, 2025. doi: 10.1101/2025.06. 24.660870.

Quanying Liu, Marco Ganzetti, Nicole Wenderoth, and Dante Mantini. Detecting large-scale brain networks using EEG: Impact of electrode density, head modeling and source localization. Frontiers in Neuroinformatics, 12:4, 2018. doi: 10.3389/fninf.2018.00004.

Patrique Fiedler, Carlos Fonseca, E. Supriyanto, Frank Zanow, and Jens Haueisen. A high-density 256-channel cap for dry electroencephalography. Human Brain Mapping, 43(4):1295–1308, 2022. doi: 10.1002/hbm.25721.

Gaetano D. Gargiulo, Paolo Bifulco, Mario Cesarelli, Alistair McEwan, Armin Nikpour, Craig Jin, Upul Gunawardana, T. Sugimoto, A. Tahir, and Y. Nie. Fully open-access passive dry electrodes BIOADC: Open-electroencephalography (EEG) re-invented. Sensors, 19(4):772, 2019. doi: 10.3390/s19040772.

Texas Instruments. ADS131M08: 8-channel, simultaneously-sampling, 24-bit, delta-sigma ADC. Datasheet SBAS950B, 2020. URL https://www.ti.com/lit/ds/sbas950b/sbas950b.pdf.

STMicroelectronics. STM32H743ZI: High-performance ARM Cortex-M7 MCU. Product brief, 2024. URL https://www.st.com/en/microcontrollers-microprocessors/stm32h743zi.html.

Michael T. Knierim, Christophe Berger, and Pierluigi Reali. Open-source concealed EEG data collection for brain-computer-interfaces neural observation through OpenBCI amplifiers with around-the-ear cEEGrid electrodes. Brain-Computer Interfaces, 8(4):161–179, 2021. doi: 10. 1080/2326263X.2021.1972633.

Michael T. Knierim, Max Schemmer, and Niclas Bauer. A simplified design of a cEEGrid earelectrode adapter for the OpenBCI biosensing platform. HardwareX, 12:e00357, 2022. doi: 10. 1016/j.ohx.2022.e00357.

Stefan Debener, Reiner Emkes, Maarten De Vos, and Martin G. Bleichner. Unobtrusive ambulatory EEG using a smartphone and flexible printed electrodes around the ear. Scientific Reports, 5: 16743, 2015. doi: 10.1038/srep16743.

George Stothart, Susanne Quadflieg, and Alexander Milton. A fast and implicit measure of semantic categorisation using steady state visual evoked potentials. Neuropsychologia, 102:11–18, 2017. doi: 10.1016/j.neuropsychologia.2017.05.025.

George Stothart, Laura J. Smith, Alexander Milton, and Elizabeth Coulthard. A passive and objective measure of recognition memory in Alzheimer’s disease using Fastball memory assessment. Brain, 144(9):2812–2825, 2021. doi: 10.1093/brain/awab154.

Table 7: Firmware rewrite plan. Phase ordering assumes a baseline capture from the stock firmware precedes any code change.

Phase | Id | Scope
Baseline | P0.1 | Power-on + CDC enumeration
P0.2 | 60 s shorted-input noise floor + 5 min eyes-
closed baseline
P0.3 | STM32 pin audit → docs/alpha-pinmap.md
Protocol | P1.0 | Wire-packet format: magic, length, seq, de-
vice µs timestamp, ADC status, 128×int24, IMU, CRC32
P1.1 | Host command protocol: | START, STOP,
SET_RATE, | SET_GAIN, | LEAD_OFF_START,
LEAD_OFF_STOP, GET_CAPS, REBOOT_DFU
Rewrite | P1.2 | Regenerate .ioc on current CubeMX; lock
USB to FS
P1.3 | Firmware | scaffold: | hal/, | drivers/,
transport/, services/
P1.4 ADS131M08 driver — per-sample CRC forwarding, drop counter, TIM/DMA CS cascade (highest risk)
P1.5 | LSM6DS3 IMU driver + interleaved IMU
| packets
P1.6 | USB-CDC framed transport, | MPU non-
cacheable DMA region, re-enabled D-Cache P1.7 Acquisition service, IWDG, RTC timestamping, boot banner, dead-code purge
P1.8 Impedance mode as first-class feature — ADS131M08 lead-off current injection + per-channel magnitude/phase
P1.9 | SD logging service + DFU-jump command
Host | P2 | Python pyserial capture → LSL outlet +
BIDS-EEG writer + FIFF writer + quality
| dashboard
P2b | BrainFlow board definition (upstream)
P2c | MNE-CPP native acquisition plugin (up-
stream PR to mne-tools/mne-cpp)
Validation | P3 | Eyes-closed 8–14 Hz alpha replication of Black
| et al. 2017
